ULAS-HiPR/lamh/firmware/src/platform/stm_f0.cpp

#if F0
#include "stm_f0.h"

I2C_HandleTypeDef hi2c1;
CAN_HandleTypeDef hcan;

void HAL_MspInit(void)
{

  __HAL_RCC_SYSCFG_CLK_ENABLE();
  __HAL_RCC_PWR_CLK_ENABLE();

  /* System interrupt init*/
  /* PendSV_IRQn interrupt configuration */
  HAL_NVIC_SetPriority(PendSV_IRQn, 3, 0);

}


/**
  * @brief CAN Initialization Function
  * @param None
  * @retval None
  */
void MX_CAN_Init(void)
{

  hcan.Instance = CAN;
  hcan.Init.Prescaler = 4;
  //hcan.Init.Mode = CAN_MODE_LOOPBACK;
  hcan.Init.Mode = CAN_MODE_NORMAL;
  hcan.Init.SyncJumpWidth = CAN_SJW_1TQ;
  hcan.Init.TimeSeg1 = CAN_BS1_13TQ;
  hcan.Init.TimeSeg2 = CAN_BS2_2TQ;
  hcan.Init.TimeTriggeredMode = DISABLE;
  hcan.Init.AutoBusOff = DISABLE;
  hcan.Init.AutoWakeUp = DISABLE;
  hcan.Init.AutoRetransmission = DISABLE;
  hcan.Init.ReceiveFifoLocked = DISABLE;
  hcan.Init.TransmitFifoPriority = DISABLE;
  if (HAL_CAN_Init(&hcan) != HAL_OK)
  {
    Error_Handler();
  }
}


/**
  * @brief CAN MSP Initialization
  * This function configures the hardware resources used in this example
  * @param hcan: CAN handle pointer
  * @retval None
  */
void HAL_CAN_MspInit(CAN_HandleTypeDef* hcan)
{
  GPIO_InitTypeDef GPIO_InitStruct = {0};
  if(hcan->Instance==CAN)
  {
    /* Peripheral clock enable */
    __HAL_RCC_CAN1_CLK_ENABLE();

    __HAL_RCC_GPIOA_CLK_ENABLE();
    /**CAN GPIO Configuration
    PA11     ------> CAN_RX
    PA12     ------> CAN_TX
    */
    GPIO_InitStruct.Pin = GPIO_PIN_11|GPIO_PIN_12;
    GPIO_InitStruct.Mode = GPIO_MODE_AF_PP;
    GPIO_InitStruct.Pull = GPIO_NOPULL;
    GPIO_InitStruct.Speed = GPIO_SPEED_FREQ_HIGH;
    GPIO_InitStruct.Alternate = GPIO_AF4_CAN;
    HAL_GPIO_Init(GPIOA, &GPIO_InitStruct);

  }

}

/**
  * @brief CAN MSP De-Initialization
  * This function freeze the hardware resources used in this example
  * @param hcan: CAN handle pointer
  * @retval None
  */
void HAL_CAN_MspDeInit(CAN_HandleTypeDef* hcan)
{
  if(hcan->Instance==CAN)
  {
    /* Peripheral clock disable */
    __HAL_RCC_CAN1_CLK_DISABLE();

    /**CAN GPIO Configuration
    PA11     ------> CAN_RX
    PA12     ------> CAN_TX
    */
    HAL_GPIO_DeInit(GPIOA, GPIO_PIN_11|GPIO_PIN_12);

  }

}

/**
  * @brief I2C1 Initialization Function
  * @param None
  * @retval None
  */
void MX_I2C1_Init(void)
{

  hi2c1.Instance = I2C1;
  hi2c1.Init.Timing = 0x00201D2B;
  hi2c1.Init.OwnAddress1 = 0;
  hi2c1.Init.AddressingMode = I2C_ADDRESSINGMODE_7BIT;
  hi2c1.Init.DualAddressMode = I2C_DUALADDRESS_DISABLE;
  hi2c1.Init.OwnAddress2 = 0;
  hi2c1.Init.OwnAddress2Masks = I2C_OA2_NOMASK;
  hi2c1.Init.GeneralCallMode = I2C_GENERALCALL_DISABLE;
  hi2c1.Init.NoStretchMode = I2C_NOSTRETCH_DISABLE;
  if (HAL_I2C_Init(&hi2c1) != HAL_OK)
  {
    Error_Handler();
  }

  /** Configure Analogue filter
  */
  if (HAL_I2CEx_ConfigAnalogFilter(&hi2c1, I2C_ANALOGFILTER_ENABLE) != HAL_OK)
  {
    Error_Handler();
  }

  /** Configure Digital filter
  */
  if (HAL_I2CEx_ConfigDigitalFilter(&hi2c1, 0) != HAL_OK)
  {
    Error_Handler();
  }
}


/**
  * @brief I2C MSP Initialization
  * This function configures the hardware resources used in this example
  * @param hi2c: I2C handle pointer
  * @retval None
  */
void HAL_I2C_MspInit(I2C_HandleTypeDef* hi2c)
{
  GPIO_InitTypeDef GPIO_InitStruct = {0};
  if(hi2c->Instance==I2C1)
  {
    __HAL_RCC_GPIOB_CLK_ENABLE();
    /**I2C1 GPIO Configuration
    PB7     ------> I2C1_SDA
    PB8     ------> I2C1_SCL
    */
    GPIO_InitStruct.Pin = GPIO_PIN_7|GPIO_PIN_8;
    GPIO_InitStruct.Mode = GPIO_MODE_AF_OD;
    GPIO_InitStruct.Pull = GPIO_NOPULL;
    GPIO_InitStruct.Speed = GPIO_SPEED_FREQ_HIGH;
    GPIO_InitStruct.Alternate = GPIO_AF1_I2C1;
    HAL_GPIO_Init(GPIOB, &GPIO_InitStruct);

    /* Peripheral clock enable */
    __HAL_RCC_I2C1_CLK_ENABLE();
  }

}

/**
  * @brief I2C MSP De-Initialization
  * This function freeze the hardware resources used in this example
  * @param hi2c: I2C handle pointer
  * @retval None
  */
void HAL_I2C_MspDeInit(I2C_HandleTypeDef* hi2c)
{
  if(hi2c->Instance==I2C1)
  {
    /* Peripheral clock disable */
    __HAL_RCC_I2C1_CLK_DISABLE();

    /**I2C1 GPIO Configuration
    PB7     ------> I2C1_SDA
    PB8     ------> I2C1_SCL
    */
    HAL_GPIO_DeInit(GPIOB, GPIO_PIN_7);

    HAL_GPIO_DeInit(GPIOB, GPIO_PIN_8);

  }

}

/**
  * @brief GPIO Initialization Function
  * @param None
  * @retval None
  */
void MX_GPIO_Init(void)
{
  GPIO_InitTypeDef GPIO_InitStruct = {0};
  /* GPIO Ports Clock Enable */
  __HAL_RCC_GPIOB_CLK_ENABLE();
  __HAL_RCC_GPIOA_CLK_ENABLE();

  /*Configure GPIO pin : PB2 */
  GPIO_InitStruct.Pin = GPIO_PIN_2;
  GPIO_InitStruct.Mode = GPIO_MODE_INPUT;
  GPIO_InitStruct.Pull = GPIO_NOPULL;
  HAL_GPIO_Init(GPIOB, &GPIO_InitStruct);

}

#endif // F0
