ULAS-HiPR/lamh/firmware/src/platform/stm_f4.cpp

#ifdef F4
#include "stm_f4.h"

I2C_HandleTypeDef hi2c1;
SPI_HandleTypeDef hspi1;

void MX_I2C1_Init()
{
    hi2c1.Instance = I2C1;
    hi2c1.Init.ClockSpeed = 100000;
    hi2c1.Init.DutyCycle = I2C_DUTYCYCLE_2;
    hi2c1.Init.OwnAddress1 = 0;
    hi2c1.Init.AddressingMode = I2C_ADDRESSINGMODE_7BIT;
    hi2c1.Init.DualAddressMode = I2C_DUALADDRESS_DISABLE;
    hi2c1.Init.OwnAddress2 = 0;
    hi2c1.Init.GeneralCallMode = I2C_GENERALCALL_DISABLE;
    hi2c1.Init.NoStretchMode = I2C_NOSTRETCH_DISABLE;

    HAL_I2C_Init(&hi2c1);
}

void HAL_I2C_MspInit(I2C_HandleTypeDef* hi2c)
{
    if (hi2c->Instance != I2C1) {
        return;
    }

    I2C_GPIO_CLK_ENABLE();
    __HAL_RCC_I2C1_CLK_ENABLE();

    GPIO_InitTypeDef GPIO_InitStruct = {0};
    GPIO_InitStruct.Pin = I2C_SCL_PIN | I2C_SDA_PIN;
    GPIO_InitStruct.Mode = GPIO_MODE_AF_OD;
    GPIO_InitStruct.Pull = GPIO_PULLUP;
    GPIO_InitStruct.Speed = GPIO_SPEED_FREQ_VERY_HIGH;
    GPIO_InitStruct.Alternate = GPIO_AF4_I2C1;
    HAL_GPIO_Init(I2C_GPIO_PORT, &GPIO_InitStruct);
}

void MX_SPI1_Init()
{
    hspi1.Instance = SPI1;

    hspi1.Init.Mode = SPI_MODE_MASTER;
    hspi1.Init.Direction = SPI_DIRECTION_2LINES;
    hspi1.Init.DataSize = SPI_DATASIZE_8BIT;
    hspi1.Init.CLKPolarity = SPI_POLARITY_LOW;
    hspi1.Init.CLKPhase = SPI_PHASE_1EDGE;
    hspi1.Init.NSS = SPI_NSS_SOFT;
    hspi1.Init.BaudRatePrescaler = SPI_BAUDRATEPRESCALER_8;
    hspi1.Init.FirstBit = SPI_FIRSTBIT_MSB;
    hspi1.Init.TIMode = SPI_TIMODE_DISABLE;
    hspi1.Init.CRCCalculation = SPI_CRCCALCULATION_DISABLE;

    HAL_SPI_Init(&hspi1);
}

void HAL_SPI_MspInit(SPI_HandleTypeDef* hspi)
{
    if (hspi->Instance != SPI1) {
        return;
    }

    SPI_GPIO_CLK_ENABLE();
    FLASH_CS_GPIO_CLK_ENABLE();
    __HAL_RCC_SPI1_CLK_ENABLE();

    GPIO_InitTypeDef GPIO_InitStruct = {0};
    GPIO_InitStruct.Pin = SPI_SCK_PIN | SPI_MISO_PIN | SPI_MOSI_PIN;
    GPIO_InitStruct.Mode = GPIO_MODE_AF_PP;
    GPIO_InitStruct.Pull = GPIO_NOPULL;
    GPIO_InitStruct.Speed = GPIO_SPEED_FREQ_VERY_HIGH;
    GPIO_InitStruct.Alternate = GPIO_AF5_SPI1;
    HAL_GPIO_Init(SPI_GPIO_PORT, &GPIO_InitStruct);

    GPIO_InitStruct.Pin = BARO_CS_PIN;
    GPIO_InitStruct.Mode = GPIO_MODE_OUTPUT_PP;
    GPIO_InitStruct.Pull = GPIO_NOPULL;
    GPIO_InitStruct.Speed = GPIO_SPEED_FREQ_VERY_HIGH;
    HAL_GPIO_Init(BARO_CS_PORT, &GPIO_InitStruct);
    HAL_GPIO_WritePin(BARO_CS_PORT, BARO_CS_PIN, GPIO_PIN_SET);

    GPIO_InitStruct.Pin = FLASH_CS_PIN;
    HAL_GPIO_Init(FLASH_CS_PORT, &GPIO_InitStruct);
    HAL_GPIO_WritePin(FLASH_CS_PORT, FLASH_CS_PIN, GPIO_PIN_SET);
}

void MX_GPIO_Init(void)
{
    ACTIVE_GPIO_CLK_ENABLE();

    GPIO_InitTypeDef GPIO_InitStruct = {0};

    GPIO_InitStruct.Pin = ACTIVE_PIN;
    GPIO_InitStruct.Mode = GPIO_MODE_OUTPUT_PP;
    GPIO_InitStruct.Pull = GPIO_NOPULL;
    GPIO_InitStruct.Speed = GPIO_SPEED_FREQ_LOW;

    HAL_GPIO_Init(ACTIVE_GPIO_PORT, &GPIO_InitStruct);
}

#endif
